dn757657/pBird-Edge/rh/rh_roller.SLDPRT

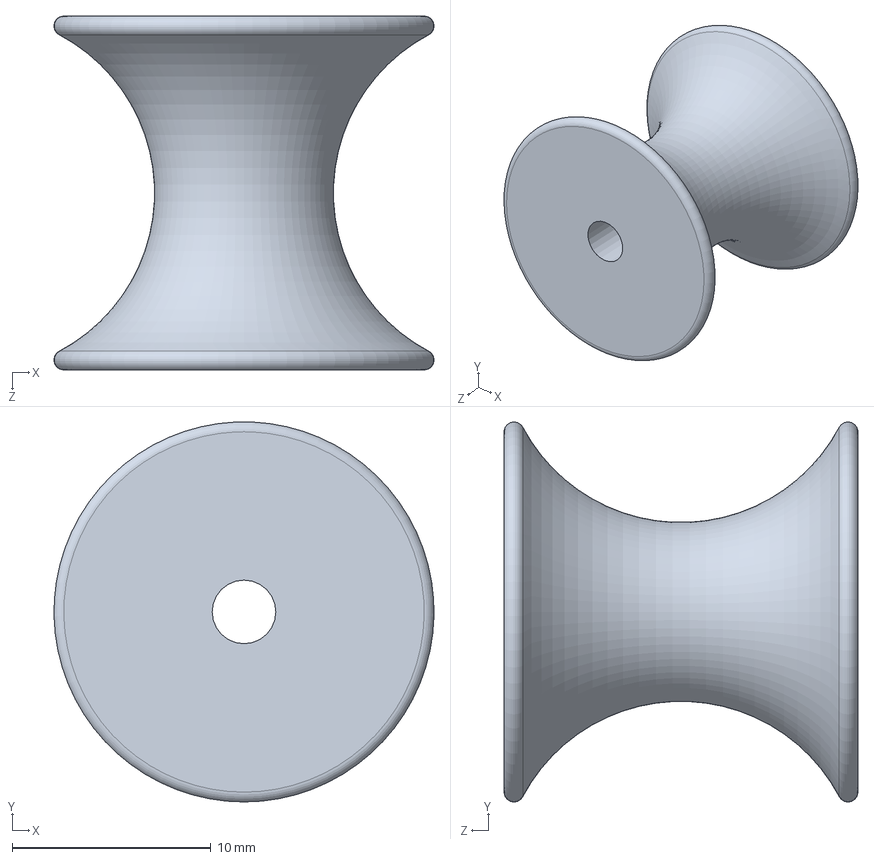
[picture p12: CAD file, 2026-01-22]
rh/rh_roller.SLDPRT
19.1 x 19.1 x 17.8 mm
