dn757657/pBird-Edge/rh/r_roller.SLDPRT

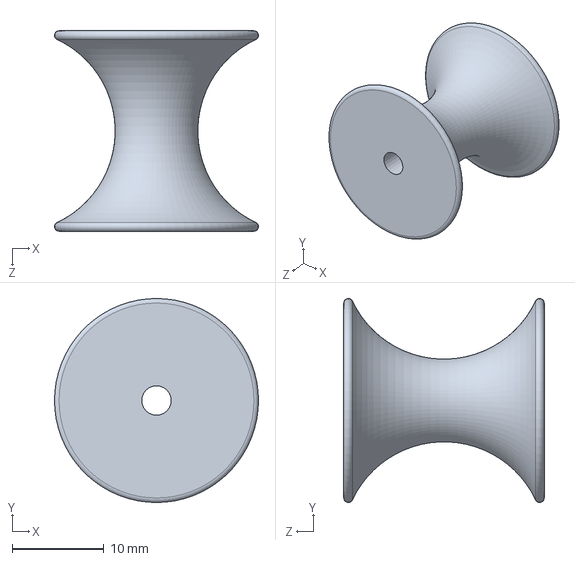
[picture p13: CAD file, 2026-01-22]
rh/r_roller.SLDPRT
22.2 x 22.2 x 21.8 mm
