dn757657/pBird-Edge/rh/m_rh_base.SLDPRT

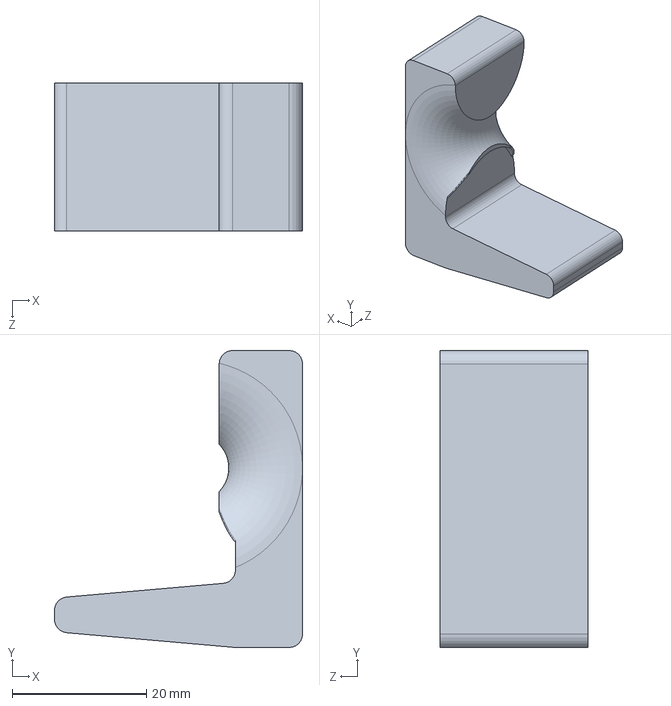
[picture p14: CAD file, 2026-01-22]
rh/m_rh_base.SLDPRT
37.0 x 44.3 x 22.0 mm
