dn757657/pBird-Edge/lh/p_lh_roller.SLDPRT

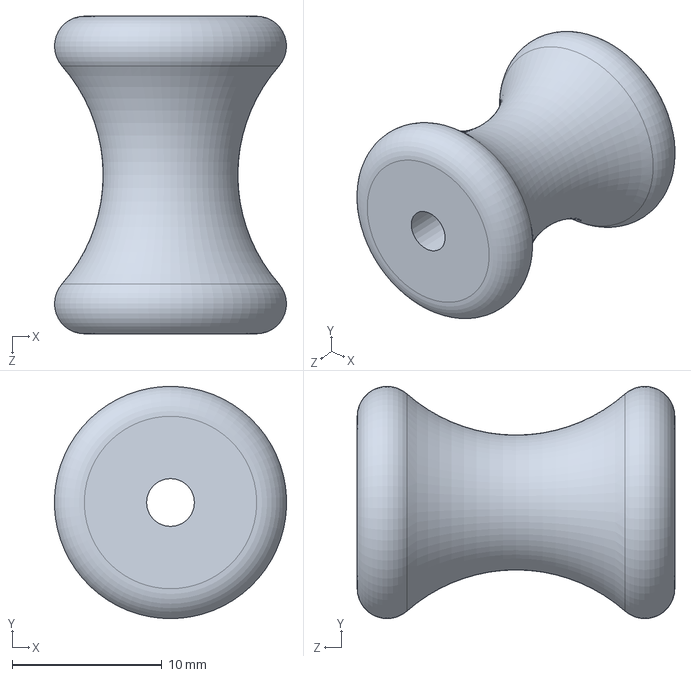
[picture p15: CAD file, 2025-10-09]
lh/p_lh_roller.SLDPRT
15.5 x 15.5 x 21.2 mm
