dn757657/pBird-Edge/rh/r_rh_base.SLDPRT

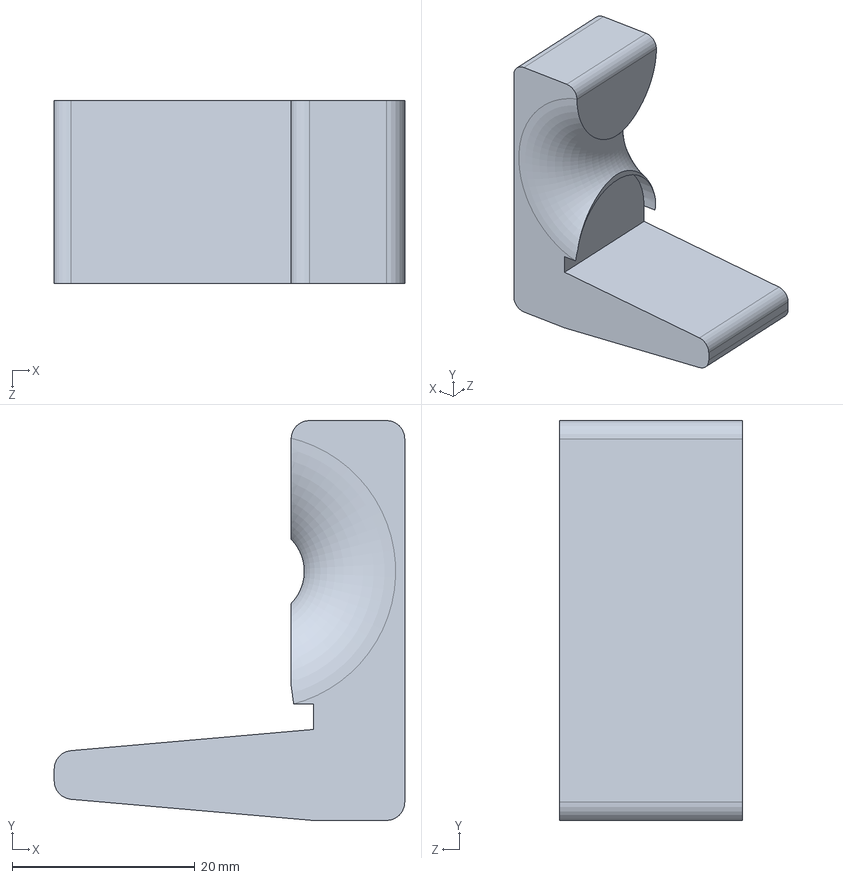
[picture p16: CAD file, 2026-01-22]
rh/r_rh_base.SLDPRT
38.3 x 43.7 x 20.0 mm
