dn757657/pBird-Edge/rh/i_rh_base.SLDPRT

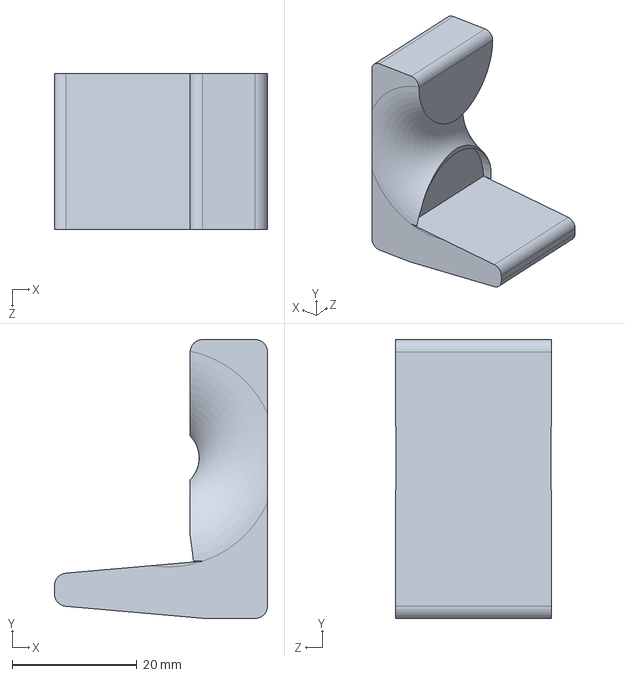
[picture p17: CAD file, 2026-01-22]
rh/i_rh_base.SLDPRT
34.2 x 44.8 x 25.0 mm
